rbreesems/flamingo/meshapp/src/pyside_imports.py

from PySide6 import QtCore  # these have not changed
from PySide6 import QtXml  # these have not changed
from PySide6.QtSvgWidgets import QGraphicsSvgItem
from PySide6.QtSvg import QSvgRenderer
from PySide6.QtTest import QTest


from PySide6.QtCore import QObject
from PySide6.QtCore import SIGNAL
from PySide6.QtCore import Slot
from PySide6.QtCore import QEvent
from PySide6.QtCore import QChildEvent
from PySide6.QtCore import QModelIndex
from PySide6.QtCore import QAbstractItemModel
from PySide6.QtCore import QAbstractTableModel
from PySide6.QtCore import QRect
from PySide6.QtCore import QPoint



# QtPrinterSupport
from PySide6.QtPrintSupport import QPrintDialog
from PySide6.QtPrintSupport import QPrinter

# QtCore
from PySide6.QtCore import Qt


# QtGui

from PySide6.QtGui import QDesktopServices
from PySide6.QtGui import QTransform
from PySide6.QtGui import QFont
from PySide6.QtGui import QIcon
from PySide6.QtGui import QColor
from PySide6.QtGui import QBrush
from PySide6.QtGui import QPen
from PySide6.QtGui import QPainter
from PySide6.QtGui import QFontMetrics
from PySide6.QtGui import QCursor
from PySide6.QtGui import QKeyEvent
from PySide6.QtGui import QStandardItemModel
from PySide6.QtGui import QStandardItem
from PySide6.QtGui import QWindow
from PySide6.QtGui import QGuiApplication
from PySide6.QtGui import QValidator
from PySide6.QtGui import QIntValidator
from PySide6.QtGui import QMouseEvent
from PySide6.QtGui import QPageSize
from PySide6.QtGui import QTextCursor
from PySide6.QtGui import QTextCharFormat



# QtWidgets
from PySide6.QtWidgets import QToolTip
from PySide6.QtWidgets import QGraphicsItemGroup
from PySide6.QtWidgets import QStyleOptionViewItem
from PySide6.QtWidgets import QItemDelegate
from PySide6.QtWidgets import QStyledItemDelegate
from PySide6.QtWidgets import QListWidget
from PySide6.QtWidgets import QListWidgetItem
from PySide6.QtWidgets import QLineEdit
from PySide6.QtWidgets import QCheckBox
from PySide6.QtWidgets import QMainWindow
from PySide6.QtWidgets import QHeaderView
from PySide6.QtWidgets import QMessageBox
from PySide6.QtWidgets import QFileDialog
from PySide6.QtWidgets import QTreeWidgetItem
from PySide6.QtWidgets import QTreeWidget
from PySide6.QtWidgets import QInputDialog
from PySide6.QtWidgets import QApplication
from PySide6.QtWidgets import QDialog
from PySide6.QtWidgets import QLabel
from PySide6.QtWidgets import QGraphicsScene
from PySide6.QtWidgets import QGraphicsView
from PySide6.QtWidgets import QGraphicsLineItem
from PySide6.QtWidgets import QGraphicsItem
from PySide6.QtWidgets import QGraphicsObject
from PySide6.QtWidgets import QGraphicsPixmapItem
from PySide6.QtWidgets import QGraphicsTextItem
from PySide6.QtWidgets import QAbstractGraphicsShapeItem
from PySide6.QtWidgets import QGraphicsRectItem
from PySide6.QtWidgets import QGraphicsEllipseItem
from PySide6.QtWidgets import QRubberBand
from PySide6.QtWidgets import QColorDialog
from PySide6.QtWidgets import QMenu
from PySide6.QtWidgets import QFontDialog
from PySide6.QtWidgets import QGraphicsColorizeEffect
from PySide6.QtWidgets import QTreeWidgetItemIterator
from PySide6.QtWidgets import QTableWidget
from PySide6.QtWidgets import QTableWidgetItem
from PySide6.QtWidgets import QWidget
from PySide6.QtWidgets import QVBoxLayout
from PySide6.QtWidgets import QMenuBar
from PySide6.QtWidgets import QStatusBar
from PySide6.QtWidgets import QTableView
from PySide6.QtWidgets import QListView
from PySide6.QtWidgets import QAbstractItemView
from PySide6.QtWidgets import QHBoxLayout
from PySide6.QtWidgets import QStyleFactory
from PySide6.QtWidgets import QComboBox
from PySide6.QtGui import QAction
from PySide6.QtCore import QUrl
from PySide6.QtMultimedia import QSoundEffect
from PySide6.QtWidgets import QToolTip
from PySide6.QtWidgets import QPlainTextEdit
from PySide6.QtWidgets import QSpinBox
from PySide6.QtWidgets import QLineEdit
from PySide6.QtWidgets import QTableWidgetSelectionRange
from PySide6.QtWidgets import QTextEdit
from PySide6.QtWidgets import QToolButton
