rbreesems/flamingo/meshapp/src/default_config.py

defaultConfigYml = """
General:
  AutoConnect: true
  LogDirectory: ""
  EnableDeviceLogEcho: false
  AutoTapback: false
  AutoTapbackKeyword: response
  AutoTapbackChannel: 0
  UseEnterToSend: false
  ConnectSound: "C:/Windows/Media/Windows Hardware Insert.wav"
  DisconnectSound: "C:/Windows/Media/Windows Hardware Remove.wav"
  MesssageInSound: "C:/Windows/Media/Windows Notify.wav"
  EnableSounds: true
GUI:
  UseDarkStyle: false
  EnableFontScaling: false
  FontDpi: 96
  WidgetScale: 1.0

"""
