rbreesems/flamingo/meshapp/src/utils.py

import os
from datetime import datetime
from pathlib import PureWindowsPath, Path, PurePath
import sys
from datetime import datetime
import posixpath
import tempfile
import threading
import time
import logging
import serial
import yaml
import re
import traceback
from copy import deepcopy
from deepdiff import DeepDiff
from default_config import defaultConfigYml
from operator import attrgetter
from pyside_imports import *



def isBroadcastId(id):
    id = convertNodeId(id)
    return id == 4294967295

def isWindowsOs():
    return sys.platform.lower().startswith('win')

def deepMerge(target, source):
    """
    Recursively merges source into target.
    """
    for key, value in source.items():
        # If both are dictionaries, recurse
        if (key in target and 
            isinstance(target[key], dict) and 
            isinstance(value, dict)):
            deepMerge(target[key], value)
        else:
            # Otherwise, just update the value
            target[key] = value
    return target

def convertNodeId(id):
    if isinstance(id, int):
        return id
    if isinstance(id, str):
        if id[0] == '!':
            try:
                id_int = int(id[1:], 16)
                return id_int
            except Exception as e:
                outputLogMessage("ERROR: Unexpected error converting node id: %s, %s/%s" % (id, sys.exc_info()[0], e), level=logging.ERROR)
        else:
            try:
                id_int = int(id, 10)
                return id_int
            except Exception as e:
                outputLogMessage("ERROR: Unexpected error converting node id: %s, %s/%s" % (id, sys.exc_info()[0], e), level=logging.ERROR)
    outputLogMessage(f"ERROR: expected either int or string for node id: {id}", level=logging.ERROR)
    return id

def filterColorCode(s):
    #the following explains color codes
    #https://www.shellhacks.com/bash-colors/
    #state
    # 0 normal
    # 1 possible start, found \e
    # 2 in esc sequence, looking for m
    #
    state = 0  #state 0, not in escape sequence
    newS = []
    esc = '\x1b'
    for i in range(len(s)):
        c = s[i]
        if c == 0:
            continue
        if state == 0:
            if c == esc:
                state = 1
                continue
            newS.append(c)
        elif state == 1:
            if c == '[':
                #definitely in escape
                state = 2
                continue
            else:
                state = 0
                newS.append(c)
        elif state == 2:
            if c == 'm':
                state = 0
            elif not (c >= '0' and c <= '9'):
                # broken esc sequence
                state = 0
    return "".join(newS)



def repairText(value):
    text = str(value or "")
    if not text:
        return ""

    if "Р" in text or "Ñ" in text:
        for source_encoding in ("cp1251", "latin1"):
            try:
                repaired = text.encode(source_encoding).decode("utf-8")
            except Exception:
                continue
            if repaired and repaired != text:
                text = repaired
                break

    return text

def describeSerialPort(port):
    return {
        "device": str(getattr(port, "device", "") or ""),
        "name": repairText(getattr(port, "name", "") or ""),
        "description": repairText(getattr(port, "description", "") or ""),
        "manufacturer": repairText(getattr(port, "manufacturer", "") or ""),
        "product": repairText(getattr(port, "product", "") or ""),
        "serialNumber": repairText(getattr(port, "serial_number", "") or ""),
        "location": repairText(getattr(port, "location", "") or ""),
        "interface": repairText(getattr(port, "interface", "") or ""),
        "hwid": repairText(getattr(port, "hwid", "") or ""),
        "vid": getattr(port, "vid", None),
        "pid": getattr(port, "pid", None),
    }


def initDefaultTreeWidgetAttributes(treeWidget, col0Width, indentation=None):
    mw = MeshAppContext.mainWindow
    treeWidget.setHeaderHidden(True)
    treeWidget.setMouseTracking(True)
    treeWidget.setFocusPolicy(QtCore.Qt.StrongFocus)
    treeWidget.setColumnCount(2)
    treeWidget.setColumnWidth(0, col0Width)
    treeWidget.setUniformRowHeights(False)
    treeWidget.setWordWrap(True)
    treeWidget.installEventFilter(mw)
    if indentation:
        treeWidget.setIndentation(indentation)


def listSerialPorts():
    try:
        from serial.tools import list_ports  # type: ignore
    except Exception:
        return []
    return [describeSerialPort(port) for port in list_ports.comports()]

def setDisplayItemDefaults(item,font=None,bg=None,fg=None):
    """
    Set values for a display item
    :param item:
    :param font:
    :param bg:
    :param fg:
    :return:
    """
    if font is not None:
        item.setFont(0, font)
    if fg is not None:
        item.setForeground(0, fg)
    if bg is not None:
        item.setBackground(0, bg)

def outputStackTrace(tb):
    """
    This function outputs the stack trace.

    """
    outputLogMessage("ERROR, Unexpected system error, stack traceback follows", level=logging.ERROR)
    lines = traceback.format_list(traceback.extract_tb(tb))
    for line in lines:
        outputLogMessage(line,level=logging.ERROR)

def doEventProcessing(force=False):
    """
    This function does event processing once a second, but not more often as this impacts performance.

    """
    

    if  MeshAppContext.disableEventProcessingFlag:
        return

    mw = MeshAppContext.mainWindow
    if mw and (mw.mainThread == threading.current_thread()):
        timeNow = time.time()
        if force or (timeNow - MeshAppContext.lastPrintTime > 1):
            # we need to process events at least once per second or else output to main window is too jumpy
            # but do not process them more often or else this impacts performance
            MeshAppContext.mainApp.processEvents()
            MeshAppContext.lastPrintTime = timeNow


def getSystemStyleDefaultColorName():
    mw = MeshAppContext.mainWindow
    if mw is None:
        #this only happens at initial startup when Main window UI elements are being initialized. After the main window is opened, this gets called
        #again during editor, canvas view initialization and the real value is set
        return 'White' #this is a dummy value
    
    if mw.systemDefaultColorName is not None:
        return mw.systemDefaultColorName
    
    pallette = mw.clearCurrentLogWindowPushButton.palette()
    cRole = mw.clearCurrentLogWindowPushButton.foregroundRole()
    defaultColor = pallette.color(cRole)
    mw.systemDefaultColorName = defaultColor.name()
    return mw.systemDefaultColorName

def getHomeDirectory():
    if isWindowsOs():
        home_path = PureWindowsPath(os.path.expanduser("~"))
        home_dir = home_path.as_posix()
    else:
        home_dir = os.path.expanduser("~")

    return home_dir


def getUserTempDirectory():
    return None

def getLocalUserColor():
    if MeshAppContext.getConfigOption("GUI:UseDarkStyle"):
        return "cyan"
    else:
        return "blue"
    
def getGetSelectedItemsFromWidget(targetWidget):
    selectedItems = []
    for i in range(0,targetWidget.topLevelItemCount()):
        # get toplevel item
        thisItem = targetWidget.topLevelItem(i)
        if thisItem.isSelected():
            selectedItems.append(thisItem)
        #if thisItem.isExpanded() and thisItem.childCount() != 0:
        #    getGetSelectedItemsFromWidgetBase(thisItem,selectedItems)

    return selectedItems

def getTemporaryFilename(base, ext='txt',useOsTempDir=False, dir=None):

    ts = datetime.now().strftime("%Y-%m-%d_%H-%M")
    filename = f"{base}_{os.getpid()}_{ts}.{ext}"
    if dir is None:
        dirname = getUserTempDirectory()
    else:
        dirname = dir
    if useOsTempDir or dirname is None:
        if isWindowsOs():
            winpath = PureWindowsPath(tempfile.gettempdir())
            dirname = winpath.as_posix()
        else:
            dirname = tempfile.gettempdir()
    return posixpath.join(dirname,filename)

def statusMessageCommon(sb,msg,level):
    
    if MeshAppContext.statusMessageSkip == 0:
        if level == logging.ERROR:
            sb.setStyleSheet("color: red;font-weight:bold")
        else:
            sb.setStyleSheet("color: %s;font-weight:normal" % getSystemStyleDefaultColorName())
        sb.showMessage(msg)
    else:
        MeshAppContext.statusMessageSkip(MeshAppContext.statusMessageSkip - 1)
    

def outputStatusMessageMainWindow(msg,mainTab=False,level=logging.INFO):
    """
    This function only updates the status bar, not the log.
    """
    mw = MeshAppContext.mainWindow
    if (mw is not None) and (mw.mainThread == threading.current_thread()):
        #By default, always display messages on status bar
        if (not mainTab) or (mainTab and mw.isTabExposed(MeshAppContext.homeTabName)):
            statusMessageCommon(mw.statusbar, msg, level)
        doEventProcessing(force=True)


def outputLogMessageThread(msg, verbosity=None, level=logging.INFO, logger=None, echoStatus=False):
    """
    This function is used by a thread other than the main thread to output a log message to the main window or the console.
    """
    mw = MeshAppContext.mainWindow
    if mw is None or (mw.mainThread == threading.current_thread()):
        #either main window not active, or we are in the main thread, ok to print.
        outputLogMessage(msg,verbosity=verbosity,level=level,logger=logger)
    else:
        mw.addAction([outputLogMessage, msg, verbosity, level, logger, echoStatus])

def outputDebugMessage(msg, textEdit):
    textEdit.append(msg)
    textEdit.verticalScrollBar().setValue(textEdit.verticalScrollBar().maximum())
    doEventProcessing()

def outputDebugMessageThread(msg, textEdit):
    mw = MeshAppContext.mainWindow
    if mw is None or (mw.mainThread == threading.current_thread()):
        outputDebugMessage(msg, textEdit)
    else:
        mw.addAction([outputDebugMessage, msg, textEdit])
        

def outputLogMessage(msg, verbosity=None, level=logging.INFO, logger=None, echoStatus=False,statusMethod=None):
    """
    This function outputs a message to the log window (either stdout in command line mode, or GUI main window).
    """
    #first, check if need to use thread version
    
    mw = MeshAppContext.mainWindow
    if level == logging.ERROR:
        MeshAppContext.errorCode = 1
    if (mw is not None) and  (mw.mainThread != threading.current_thread()):
        #have to use different version.
        outputLogMessageThread(msg, verbosity=verbosity, level=level, logger=logger, echoStatus=echoStatus)
    else:
        if logger is None:
            logger = MeshAppContext.defaultLogger
            if logger is not None:
                logger.verbosity = verbosity
                logger.log(level,msg)
        else:
            logger.verbosity = verbosity
            logger.log(level,msg)
    if echoStatus:
        if statusMethod is not None:
            statusMethod(msg,level=level)
        else:
            outputStatusMessageMainWindow(msg, mainTab=False, level=level)

def logNodeMessage(msg):
    """
    Used only to log node messages
    """
    logger = MeshAppContext.messageLogger
    if logger is not None:
        logger.log(logging.INFO,msg)

def getNodeLongShortNames(nodeId):
    node = MeshAppContext.getNodeById(nodeId)
    if node is None:
        longName = 'n/a'
        shortName = 'n/a'
    else:
        longName = node.longName
        shortName = node.shortName 
        if longName == "":
            longName = 'n/a'
        if shortName == "":
            shortName = 'n/a'
    return longName, shortName


class Node(object):

    def __init__(self, id=""):
        self.id = convertNodeId(id)   #this is always the decimal ID
        self.longName = ""
        self.shortName = ""
        self.role = ""
        self.batteryLevel = 0
        self.voltage = 0
        self.uptimeSeconds = 0
        self.lastUpdate = 0
        self.lastUpdateFmt = ""
        self.hops = 0
        self.traceRoutes = []

    def updateNodeTimeStamp(self):
        self.lastUpdate = time.time()
        self.lastUpdateFmt = f"{datetime.now(): %H:%M:%S %m-%d-%Y}"


    def getDisplayName(self):
        if self.longName:
            return self.longName
        else:
            return str(self.id)

    def toDict(self):
        aDict = {}
        for attr, value in vars(self).items():
            if attr == 'traceRoutes':
                continue
            aDict[attr] = value
        return aDict
    
    def description(self):

        desc = []
        attrList = list(vars(self).keys())
        attrList.sort()
        for attr in attrList:
            value = getattr(self, attr)
            if attr == 'traceRoutes' and len(value) > 0:
                for traceRoute in value:
                    trList = [[f"Traceroute {traceRoute[0]} "]]
                    pair = traceRoute[1]
                    fwdHops = pair[0][0]
                    nodeHops = pair[0][1]
                    fwdList = [[fwdHops]]
                    for nodeHop in nodeHops:
                        fwdList.append([nodeHop])
                    trList.append(fwdList)

                    backHops = pair[1][0]
                    nodeHops = pair[1][1]
                    backList = [[backHops]]
                    for nodeHop in nodeHops:
                        backList.append([nodeHop])
                    trList.append(backList)
                    desc.append(trList)
            else:
                desc.append([f"{attr} : {value}"])
        return desc


class ActionItem(object): 
    
    def __init__(self, func, posArgs = None, optArgs = None):
        self.func = func
        self.posArgs = posArgs # always a list
        self.optArgs= optArgs  # always a dict

class MeshAppContext(object):

    mainWindow = None
    mainApp = None
    logfile = None
    messageLogFile = None
    defaultLogger = None
    defaultVerbosity = 0
    systemDefaultColorName = None
    disableEventProcessingFlag = False
    lastPrintTime = 0
    errorCode = 0
    homeTabName = 'Home'
    statusMessageSkip = 0
    welcomeShown = False
    isMeshConnected = False
    configData = None
    configDataOrg = None
    deviceLogEchoEnabled = False   # duplicate this from config for performance
    messageLogger = None
    nodeDb: dict[int, dict] = {}
    # node colors for everthing except local node
    colorIndex = 0
    #                  green
    nodeColorList = ["#2A7822", "#A1A17D", "#45B5CE", "#8D58CC"]
    #                  lgreen
    nodeColorListDark =  ["#B2D19B", "#D6D6A7", "#A6E2F0", "#C8A8F0"]
    nodeColorMap: dict[int, str] = {}
    localNodeId = 0
    localNodeLongName = ""
    localNodeShortName = ""

    @classmethod
    def getNextNodeColor(self):
        if MeshAppContext.getConfigOption("GUI:UseDarkStyle"):
            colorList = self.nodeColorListDark
        else:
            colorList = self.nodeColorList
        color = colorList[self.colorIndex]
        self.colorIndex += 1
        if self.colorIndex == len(colorList):
            self.colorIndex = 0
        return color
    
    @classmethod
    def getNodeColor(self, id):
        id = convertNodeId(id)
        if id not in self.nodeColorMap:
            if id == self.localNodeId:
                self.nodeColorMap[id] = getLocalUserColor()
            else:
                self.nodeColorMap[id] = self.getNextNodeColor()
        return self.nodeColorMap[id]

    @classmethod
    def getConfigOption(self, configOption, default=None):
        if self.configData is None:
            return default
        if not isinstance(self.configData, dict):
            return default
        keylist = configOption.split(':')
        currentDict = self.configData
        value = default
        for i in range(len(keylist)):
            if i == len(keylist) - 1:
                # at last key
                value = currentDict.get(keylist[i], default)
                break
            else:
                currentDict = currentDict.get(keylist[i], None)
                if currentDict is None or not isinstance(currentDict, dict):
                    return default
        return value
    
    @classmethod
    def setConfigOption(self, configOption, value):
        if self.configData is None:
            return
        if not isinstance(self.configData, dict):
            return
        keylist = configOption.split(':')
        currentDict = self.configData
        for i in range(len(keylist)):
            if i == len(keylist) - 1:
                # at last key
                currentDict[keylist[i]] = value
                break
            else:
                currentDict = currentDict.get(keylist[i], None)
                if currentDict is None or not isinstance(currentDict, dict):
                    return
        return
    
    @classmethod
    def getConfigDirPath(self):
        configDir = posixpath.join(getHomeDirectory(), '.flamingo_meshapp')
        Path(configDir).mkdir(exist_ok=True)
        return configDir

    @classmethod
    def getConfigFilePath(self):
        return posixpath.join(self.getConfigDirPath(), 'meshapp_config.yml')
    
    @classmethod
    def loadConfigFile(self, configFilePath=None):
        defaultConfig = yaml.safe_load(defaultConfigYml)
        if configFilePath is None:
            configFilePath = self.getConfigFilePath()
        if not posixpath.isfile(configFilePath):
            self.configData = defaultConfig
            return  #no config data
        newConfig = {}

        try:
            with open(configFilePath, 'r') as file:
                newConfig = yaml.safe_load(file) # Use safe_load to prevent arbitrary code execution
                self.configDataOrg = deepcopy(newConfig)
                print(f"Configdata loaded from {configFilePath}")
        except Exception as e:
            print("ERROR: Unexpected error parsing yml file: %s, %s/%s" % (configFilePath, sys.exc_info()[0], e))
            self.configData = defaultConfig
            return
        
        # merge newConfig into defaultConfig recursively
        # do this because defaultConfig may have new settings that
        # are not in a user's config
        deepMerge(defaultConfig, newConfig)
        self.configData = defaultConfig
        

    @classmethod 
    def saveConfigFile(self, configFilePath=None):
        if configFilePath is None:
            configFilePath = self.getConfigFilePath()
        try:
            diffs = DeepDiff(self.configData, self.configDataOrg)
            if len(diffs) > 0 or not posixpath.isfile(configFilePath):
                with open(configFilePath, 'w') as file:
                    yaml.safe_dump(self.configData,file) # Use safe_load to prevent arbitrary code execution
                
                    print(f"Configdata saved to {configFilePath}")
        except Exception as e:
            print("ERROR: Unexpected error writing yml file: %s, %s/%s" % (configFilePath, sys.exc_info()[0], e))
            return
        
    @classmethod
    def nodeDbToDict(self):
        nodeDict = {}
        for id, node in self.nodeDb.items():
            nodeDict[id] = node.toDict()
        return nodeDict
    
    @classmethod
    def addNodeToDb(self, id, node):
        self.nodeDb[id] = node

    @classmethod
    def dictToNode(self, aDict):
        aNode = Node(id=0) # pass in a dummy ID, this will get overwritten
        for key, value in aDict.items():
            setattr(aNode, key, value)
        return aNode

    @classmethod
    def dictToNodeDb(self, aDict):
        self.nodeDb = {}
        if aDict is not None:
            for key, value in aDict.items():
                self.addNodeToDb(key, self.dictToNode(value))

    @classmethod
    def getNodeDbFilePath(self):
        return posixpath.join(self.getConfigDirPath(), 'meshapp_nodedb.yml')
    
    @classmethod
    def getNodeList(self, filter=None, sort=None, filterOldNodes=False):
        nodeList =  []
        pat = None
        if filter:
            try:
                pat = re.compile(filter)
            except:
                pat = None
        cutoffTime = int(time.time()) - 24*60*60
        for node in self.nodeDb.values():
            if filterOldNodes and (node.lastUpdate < cutoffTime):
                continue
            if pat:
                if re.match(pat, node.longName):
                    nodeList.append(node)
            else:
                nodeList.append(node)
        if sort:
            nodeList = sorted(nodeList, key=attrgetter(sort))
        return nodeList
    
  
    @classmethod
    def getNodeCount(self):
        return len(self.nodeDb)
    
    @classmethod
    def loadNodeDb(self):
        nodedbFilePath = self.getNodeDbFilePath()
        if not posixpath.isfile(nodedbFilePath):
            return  #no config data
        try:
            with open(nodedbFilePath, 'r') as file:
                aDict = yaml.safe_load(file) # Use safe_load to prevent arbitrary code execution
                
                self.dictToNodeDb(aDict)     
                print(f"NodeDb loaded from {nodedbFilePath}")
        except Exception as e:
            print("ERROR: Unexpected error parsing yml file: %s, %s/%s" % (nodedbFilePath, sys.exc_info()[0], e))
            return
        
    @classmethod 
    def saveNodeDb(self, configFilePath=None):
        nodedbFilePath = self.getNodeDbFilePath()
        try:
            with open(nodedbFilePath, 'w') as file:
                    nodeDict = MeshAppContext.nodeDbToDict()
                    yaml.safe_dump(nodeDict,file)
                    print(f"NodeDb saved to {nodedbFilePath}")
        except Exception as e:
            print("ERROR: Unexpected error writing yml file: %s, %s/%s" % (nodedbFilePath, sys.exc_info()[0], e))
            return
        
    @classmethod
    def getMaxHopLimitForTraceRoute(self):
        return 18
        
    @classmethod
    def addLocalNodeToDb(self):
        """
        Add the locally connected node to the DB, called on connection
        """
        info = self.mainWindow.serialInterface.getMyNodeInfo()
        id = info.get('num',None)
        if id is None:
            return
        newNode = Node(id=id)
        self.nodeDb[newNode.id] = newNode
        self.localNodeId = convertNodeId(id)
        user = info.get('user',None)
        if user:
            newNode.longName = user.get('longName','')
            newNode.shortName = user.get('shortName','')
            self.localNodeLongName = newNode.longName
            self.localNodeShortName = newNode.shortName
        self.updateNodeTimeStamp(id)

    @classmethod
    def addEmptyNode(self,id):
        """
        Called when packet arrives for from/to id values
        Add nodes if not in DB, update lastUpdate time
        """
        id = convertNodeId(id)
        if isBroadcastId(id):
            return
        if id not in self.nodeDb:
            self.addNodeToDb(id, Node(id=id))
        self.nodeDb[id].lastUpdate = time.time()
        return

    @classmethod
    def getNodeById(self,id):
        id = convertNodeId(id)
        if isBroadcastId(id):
            return None
        retVal = self.nodeDb.get(id,None)
        return retVal
    
    @classmethod
    def getNodeByLongname(self, longName):
        for node in self.nodeDb.values():
            if node.longName == longName:
                return node
        return None
    
    @classmethod
    def handleAckPacket(self, packet):
        if not (packet.get('to',None) == self.localNodeId):
            return
        fromId = packet.get('from',None)
        #priority = packet.get('priority', None)
        #if priority != 'ACK':
        #    return
        decoded = packet.get('decoded', None)
        if decoded is None:
            return
        portnum = decoded.get('portnum', None)
        if portnum != 'ROUTING_APP':
            return
        requestId = decoded.get('requestId', None)
        if requestId is None:
            return
       
        routing = decoded.get('routing', None)
        if routing is None:
            return
        errorReason = routing.get('errorReason', None)
        if errorReason is None:
            return
        # at this point, have ACK routing packet.
        # Call the main window to handle this
        self.mainWindow.handleMessageAck(requestId, errorReason, fromId)
        return
    
    @classmethod
    def updateNodeTimeStamp(self, id):
        node = self.getNodeById(id)
        if node:
            node.updateNodeTimeStamp()

    @classmethod
    def updateNodeDbFromPacket(self, packet):
        fromId = packet.get('from',None)
        if fromId:
            self.addEmptyNode(fromId)
        toId = packet.get('to',None)
        if toId:
            self.addEmptyNode(toId)
        self.updateNodeTimeStamp(fromId)
        self.updateNodeTimeStamp(toId)
        decoded = packet.get('decoded', None)
        if decoded is None:
            return
        portnum = decoded.get('portnum', None)
        if portnum == 'TELEMETRY_APP':
            telemetry = decoded.get('telemetry', None)
            if telemetry:
                deviceMetrics = telemetry.get('deviceMetrics', None)
                node = self.getNodeById(fromId)
                if deviceMetrics:
                    batteryLevel = deviceMetrics.get('batteryLevel', None)
                    if isinstance(batteryLevel, int) and node:
                        node.batteryLevel = batteryLevel
                    uptimeSeconds = deviceMetrics.get('uptimeSeconds', None)
                    if (isinstance(uptimeSeconds, int)  or isinstance(uptimeSeconds, float)) and node:
                        node.uptimeSeconds = uptimeSeconds
                    voltage =  deviceMetrics.get('voltage', None)
                    if (isinstance(voltage, int)  or isinstance(voltage, float)) and node:
                        node.voltage = voltage
                    # update the nodes tab since trace route is updated
                    self.mainWindow.updateNodesTab()
                    # update status bar as this may have been an explicit telemetry request
                    outputLogMessage(f"Telemetry received for node {node.longName}. ", echoStatus=True)
        elif portnum == 'NODEINFO_APP':
            user = decoded.get('user', None)
            if user:
                id = user.get('id',None)
                if id:
                    node = self.getNodeById(id)
                    if node:
                        oldLongName = f"{node.longName}"
                        node.longName = user.get('longName', '')
                        oldShortName = f"{node.shortName}"
                        node.shortName = user.get('shortName', '')
                        nameChanged = oldLongName != node.longName or oldShortName != node.shortName
                        node.role = user.get('role', '')
                        outputLogMessage(f"NODEINFO received:  { user.get('shortName', '')} / {user.get('longName', '')}")
                        if self.mainWindow:
                            self.mainWindow.updateDmTabsComboBox()
                            self.mainWindow.updateNodesTab()
                            if nameChanged:
                                self.mainWindow.regenerateMessages(node.id)

        elif portnum == 'TRACEROUTE_APP' and self.mainWindow.activeTraceRoute and toId == self.localNodeId:
            # parse and save the traceroute
            trDict = decoded.get('traceroute', None)
            endNode = self.getNodeById(self.mainWindow.activeTraceRoute)
            if trDict and endNode:
                route = trDict.get('route', None)
                snrTowards = trDict.get('snrTowards', None)
                routeBack = trDict.get('routeBack', None)
                snrBack = trDict.get('snrBack', None)
                forwardPath = ""
                backwardPath = ""
                startNode = self.localNodeLongName
                if snrTowards:
                    if route is None:
                        # special case, 0 hop
                        hops = 0
                        snr = snrTowards[0]/4
                        forwardPath = [f"Forward ({hops} hops)", [f"{startNode}", f"{endNode.longName} ({snr:.2f}dB)"]]
                    else:
                        hops = len(route)
                        forwardPath = [f"Forward ({hops} hops)"]
                        nodeList = [f"{startNode}"]
                        for i in range(0, len(route)):
                            node = self.getNodeById(route[i])
                            if node:
                                snr = snrTowards[i]/4
                                nodeList.append(f"{node.longName}  ({snr:.2f}dB)")
                        # add in the last node
                        snr = snrTowards[len(snrTowards)-1]/4
                        nodeList.append(f"{endNode.longName}  ({snr:.2f}dB)")
                        forwardPath.append(nodeList)
                if snrBack:
                    if routeBack is None:
                        # special case, 0 hop
                        hops = 0
                        snr = snrTowards[0]/4
                        backwardPath = [f"Backward ({hops} hops)", [f"{endNode.longName}", f"{startNode} ({snr:.2f}dB)"]]
                    else:
                        hops = len(routeBack)
                        backwardPath = [f"Backward ({hops} hops)"]
                        nodeList = [f"{endNode.longName}"]
                        for i in range(0, len(routeBack)):
                            node = self.getNodeById(routeBack[i])
                            if node:
                                snr = snrTowards[i]/4
                                nodeList.append(f"{node.longName}  ({snr:.2f}dB)")
                        # add in the last node
                        snr = snrBack[len(snrBack)-1]/4
                        nodeList.append(f"{startNode}  ({snr:.2f}dB)")
                        backwardPath.append(nodeList)
                # Add this traceroute
                self.mainWindow.activeTraceRoute = None
                endNode.traceRoutes.insert(0,[endNode.lastUpdateFmt,[forwardPath,backwardPath]])
                # update the nodes tab since trace route is updated
                self.mainWindow.updateNodesTab()
            return
